ClenonWolf/ESP-DIN-BLT/Schematics/ESP-DIN-BLT.kicad_sch

## KiCad design Schematics/ESP-DIN-BLT.kicad_sch (2024-11-28)

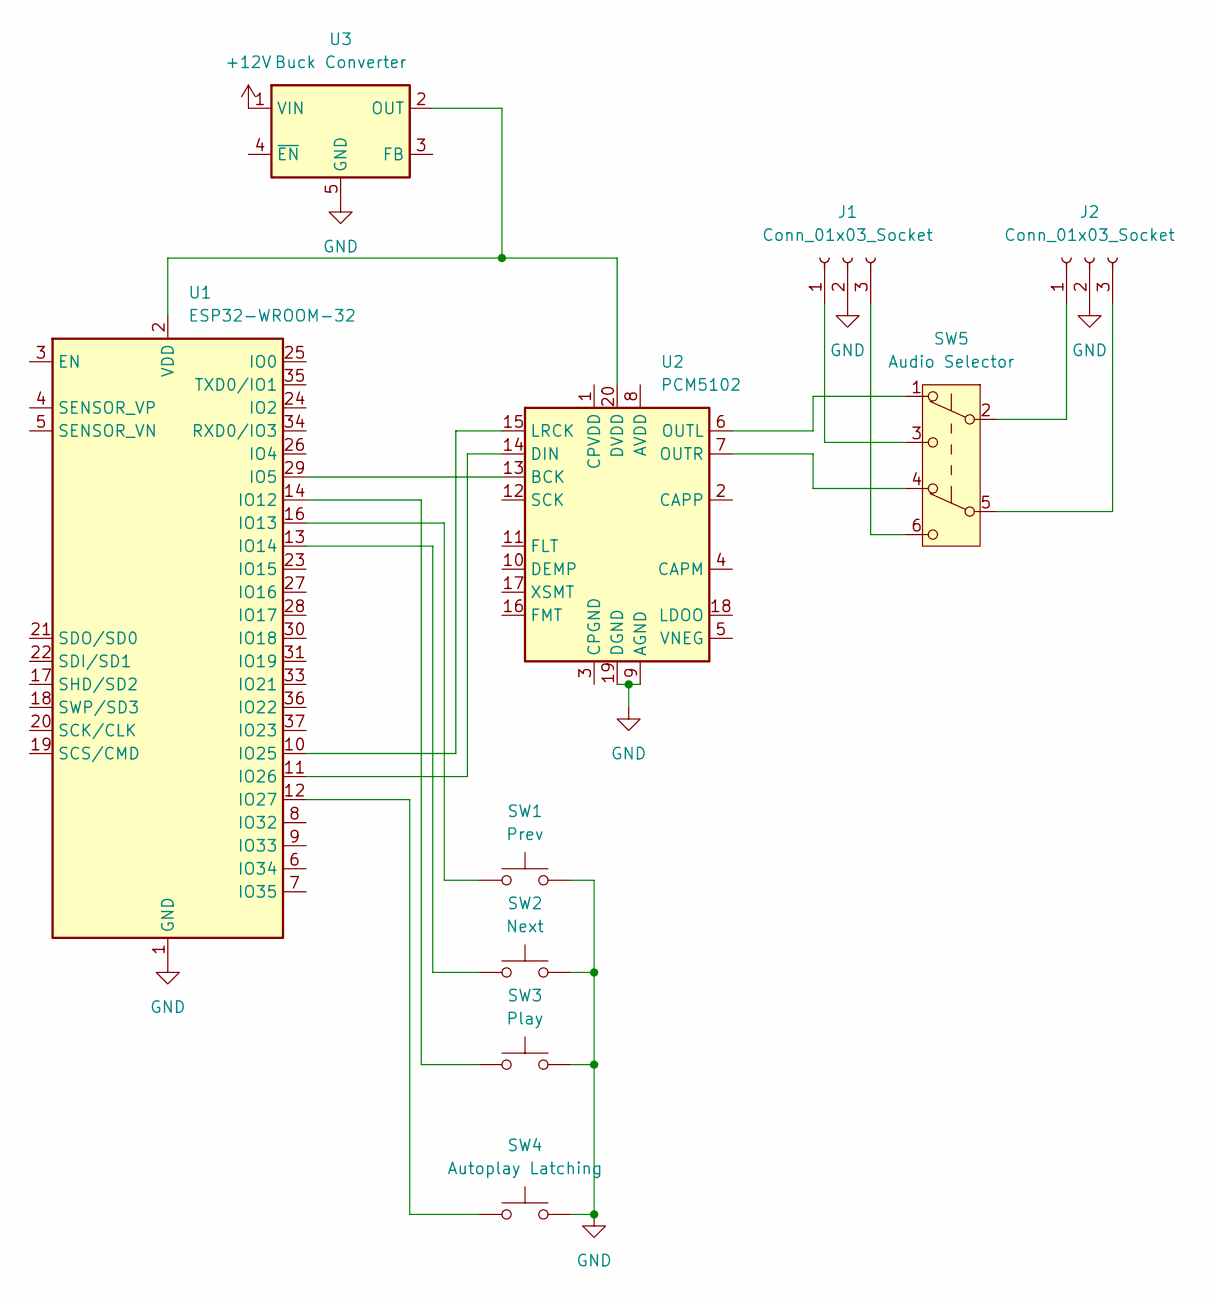
[picture p2: schematic ESP-DIN-BLT.kicad_sch]

Parts:
J1, J2: Conn_01x03_Socket
SW1: Prev
SW2: Next
SW3: Play
SW4: Autoplay Latching
SW5: Audio Selector
U1: ESP32-WROOM-32
U2: PCM5102; TSSOP-20_4.4x6.5mm_P0.65mm
U3: Buck Converter; SOIC-8_3.9x4.9mm_P1.27mm

Connections:
+12V: U3.1 (VIN)
GND: J1.2, J2.2, SW1.2, SW2.2, SW3.2, SW4.2, U1.1 (GND), U1.15 (GND), U1.38 (GND), U1.39 (GND), U2.9 (AGND), U2.19 (DGND), U3.5 (GND), U3.6 (GND), U3.7 (GND), U3.8 (GND)
unnamed: J1.1, SW5.3 (C)
unnamed: J1.3, SW5.6 (C)
unnamed: J2.1, SW5.2 (B)
unnamed: J2.3, SW5.5 (B)
unnamed: SW1.1, U1.16 (IO13)
unnamed: SW2.1, U1.13 (IO14)
unnamed: SW3.1, U1.14 (IO12)
unnamed: SW4.1, U1.12 (IO27)
unnamed: SW5.1 (A), U2.6 (OUTL)
unnamed: SW5.4 (A), U2.7 (OUTR)
unnamed: U1.2 (VDD), U2.20 (DVDD), U3.2 (OUT)
unnamed: U1.10 (IO25), U2.15 (LRCK)
unnamed: U1.11 (IO26), U2.14 (DIN)
unnamed: U1.29 (IO5), U2.13 (BCK)
